gzalo/ncomputing-l130/pcb/l130.kicad_sch

## KiCad design pcb/l130.kicad_sch (2023-08-18, an earlier design)

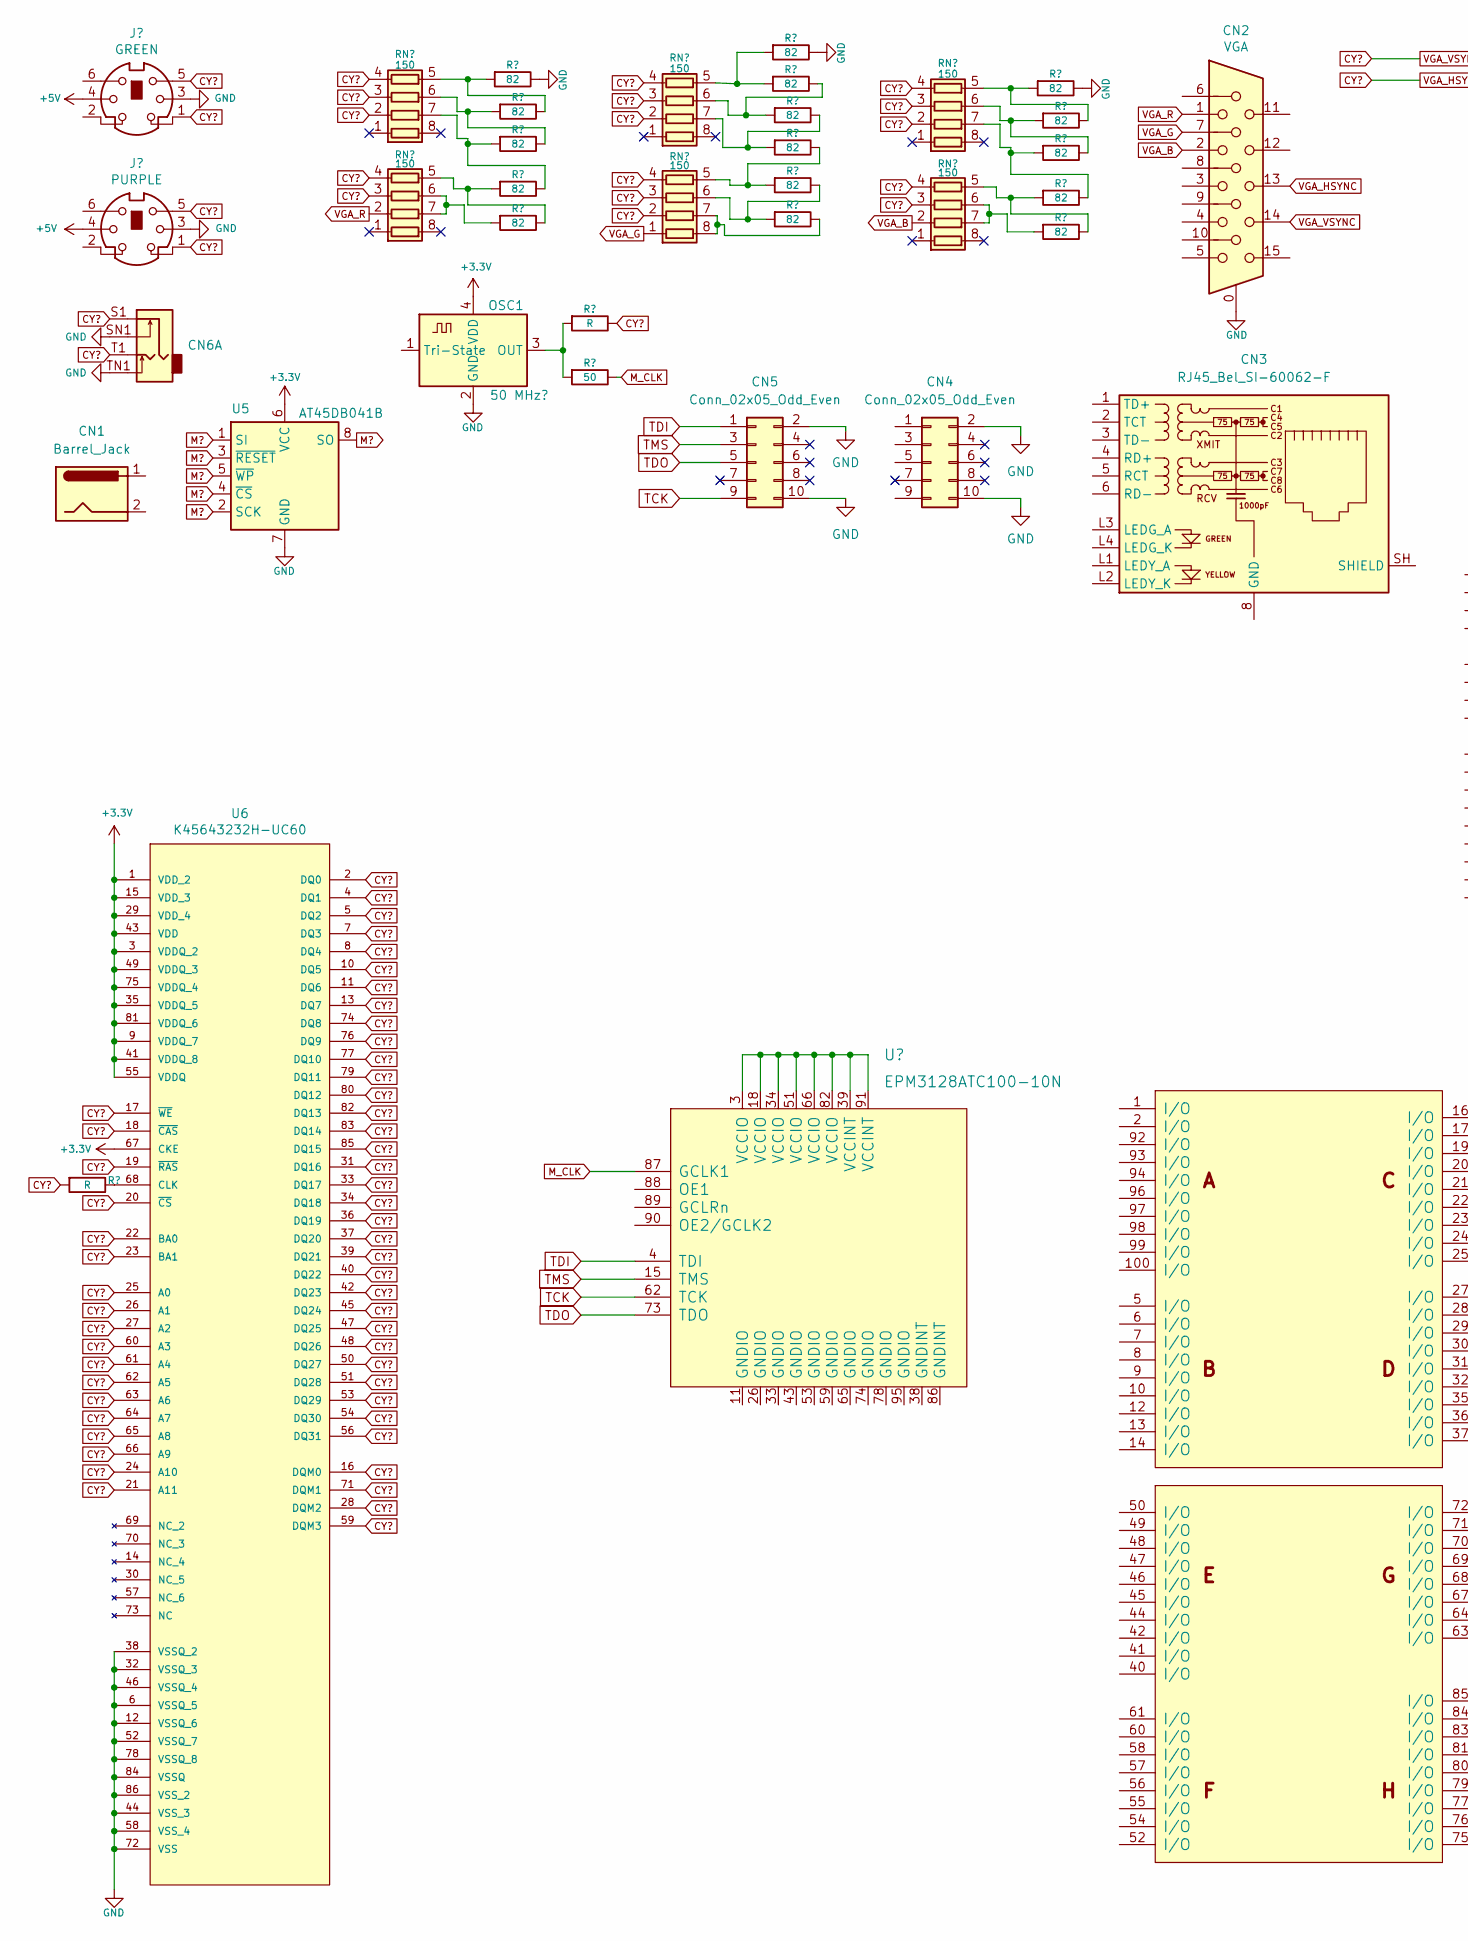
[picture p23: schematic l130.kicad_sch, part in row 1, column 1]

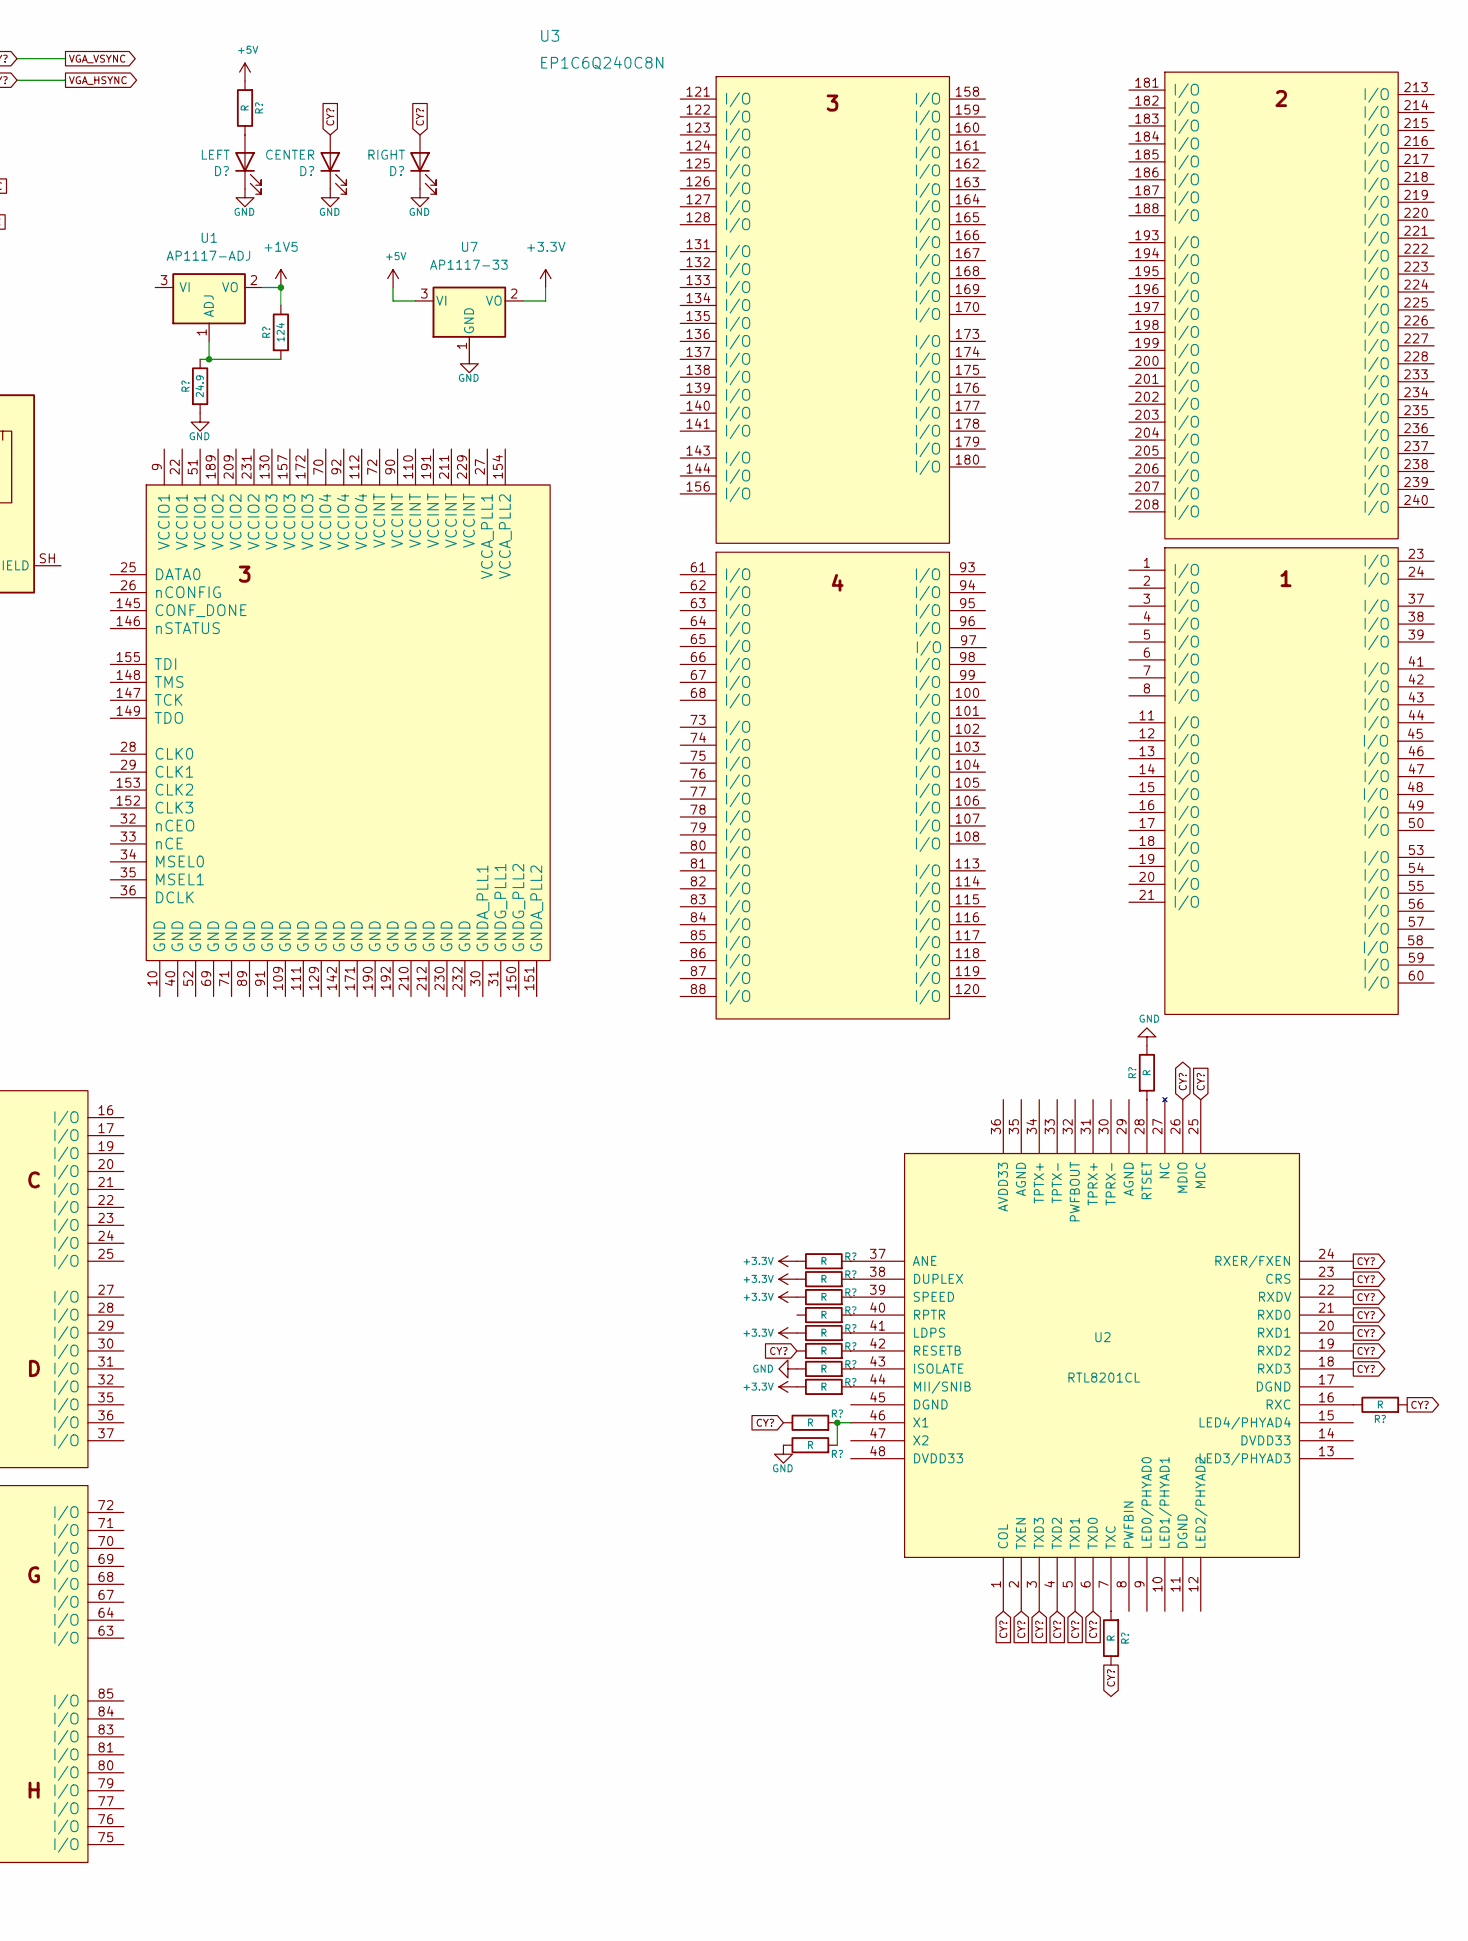
[picture p24: schematic l130.kicad_sch, part in row 1, column 2]

Parts:
CN1: Barrel_Jack
CN2: VGA
CN3: RJ45_Bel_SI-60062-F
CN4, CN5: Conn_02x05_Odd_Even
CN6: AudioJack2_Dual_Switch
OSC1: 50 MHz?; Oscillator_SMD_Abracon_ASCO-4Pin_1.6x1.2mm
U1: AP1117-ADJ; SOT-223-3_TabPin2
U2: RTL8201CL; MODULE
U3: EP1C6Q240C8N
U5: AT45DB041B; SOIC-8_5.275x5.275mm_P1.27mm
U6: K45643232H-UC60; SOP50P1176X120-86N
U7: AP1117-33; SOT-223-3_TabPin2

Connections:
CY?: CN2.13, CN2.14, CN6.S1, CN6.T1, U2.1 (COL), U2.2 (TXEN), U2.3 (TXD3), U2.4 (TXD2), U2.5 (TXD1), U2.6 (TXD0), U2.18 (RXD3), U2.19 (RXD2), U2.20 (RXD1), U2.21 (RXD0), U2.22 (RXDV), U2.23 (CRS), U2.24 (RXER/FXEN), U2.25 (MDC), U2.26 (MDIO), U6.2 (DQ0), U6.4 (DQ1), U6.5 (DQ2), U6.7 (DQ3), U6.8 (DQ4), U6.10 (DQ5), U6.11 (DQ6), U6.13 (DQ7), U6.16 (DQM0), U6.17 (~WE), U6.18 (~CAS), U6.19 (~RAS), U6.20 (~CS), U6.21 (A11), U6.22 (BA0), U6.23 (BA1), U6.24 (A10), U6.25 (A0), U6.26 (A1), U6.27 (A2), U6.28 (DQM2), U6.31 (DQ16), U6.33 (DQ17), U6.34 (DQ18), U6.36 (DQ19), U6.37 (DQ20), U6.39 (DQ21), U6.40 (DQ22), U6.42 (DQ23), U6.45 (DQ24), U6.47 (DQ25), U6.48 (DQ26), U6.50 (DQ27), U6.51 (DQ28), U6.53 (DQ29), U6.54 (DQ30), U6.56 (DQ31), U6.59 (DQM3), U6.60 (A3), U6.61 (A4), U6.62 (A5), U6.63 (A6), U6.64 (A7), U6.65 (A8), U6.66 (A9), U6.71 (DQM1), U6.74 (DQ8), U6.76 (DQ9), U6.77 (DQ10), U6.79 (DQ11), U6.80 (DQ12), U6.82 (DQ13), U6.83 (DQ14), U6.85 (DQ15)
M?: U5.1 (SI), U5.2 (SCK), U5.3 (~RESET), U5.4 (~CS), U5.5 (~WP), U5.8 (SO)
unnamed: U6.1 (VDD_2), U6.3 (VDDQ_2), U6.9 (VDDQ_7), U6.15 (VDD_3), U6.29 (VDD_4), U6.35 (VDDQ_5), U6.41 (VDDQ_8), U6.43 (VDD), U6.49 (VDDQ_3), U6.55 (VDDQ), U6.75 (VDDQ_4), U6.81 (VDDQ_6)
unnamed: U6.6 (VSSQ_5), U6.12 (VSSQ_6), U6.32 (VSSQ_3), U6.38 (VSSQ_2), U6.44 (VSS_3), U6.46 (VSSQ_4), U6.52 (VSSQ_7), U6.58 (VSS_4), U6.72 (VSS), U6.78 (VSSQ_8), U6.84 (VSSQ), U6.86 (VSS_2)
TCK: CN5.9
TDI: CN5.1
TDO: CN5.5
TMS: CN5.3
VGA_B: CN2.2
VGA_G: CN2.7
VGA_R: CN2.1
