gzalo/ncomputing-l130/pin-flex/pin-flex.kicad_sch

## KiCad design pin-flex/pin-flex.kicad_sch (2025-07-04)

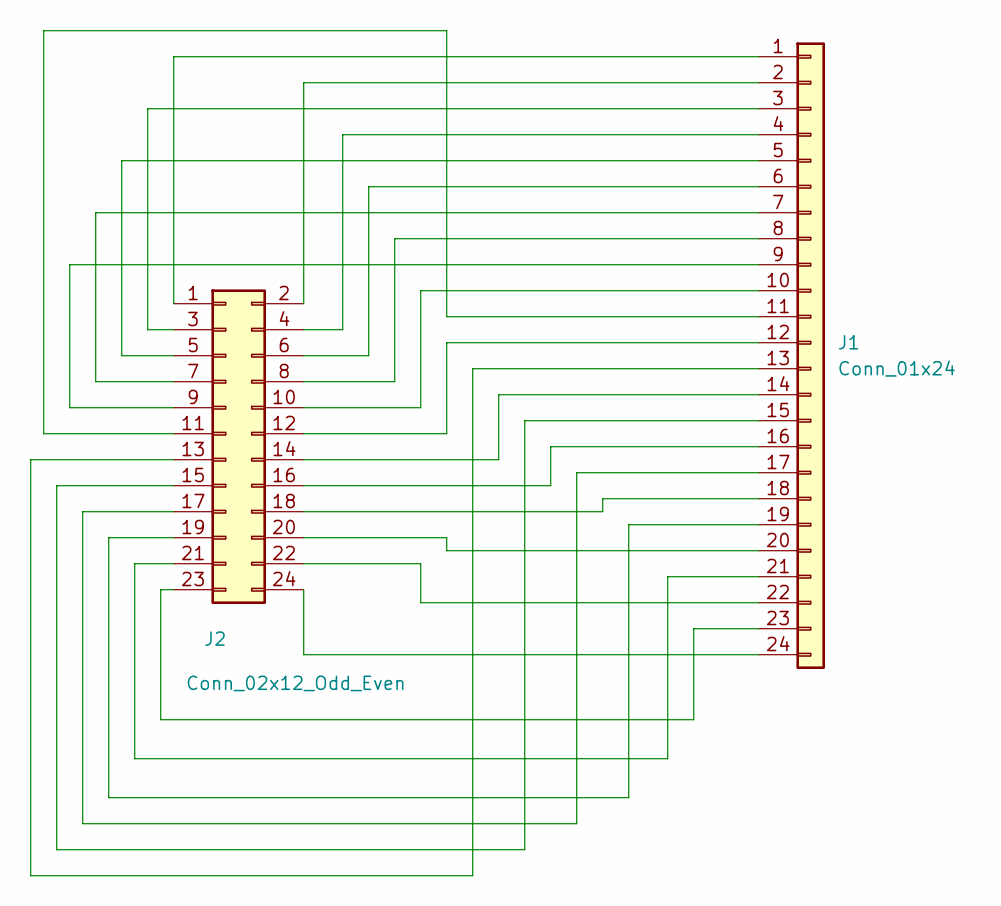
[picture p25: schematic pin-flex.kicad_sch]

Parts:
J1: Conn_01x24; 24-pin-0.5
J2: Conn_02x12_Odd_Even; PinHeader_2x12_P2.54mm_Vertical

Connections:
unnamed: J1.1, J2.1
unnamed: J1.2, J2.2
unnamed: J1.3, J2.3
unnamed: J1.4, J2.4
unnamed: J1.5, J2.5
unnamed: J1.6, J2.6
unnamed: J1.7, J2.7
unnamed: J1.8, J2.8
unnamed: J1.9, J2.9
unnamed: J1.10, J2.10
unnamed: J1.11, J2.11
unnamed: J1.12, J2.12
unnamed: J1.13, J2.13
unnamed: J1.14, J2.14
unnamed: J1.15, J2.15
unnamed: J1.16, J2.16
unnamed: J1.17, J2.17
unnamed: J1.18, J2.18
unnamed: J1.19, J2.19
unnamed: J1.20, J2.20
unnamed: J1.21, J2.21
unnamed: J1.22, J2.22
unnamed: J1.23, J2.23
unnamed: J1.24, J2.24
