gzalo/ncomputing-l130/fpga_vga/char_rom.vhd

library ieee;
use ieee.std_logic_1164.all;
use ieee.numeric_std.all;

entity char_rom is
	port(
		clk: in std_logic;
		char: in std_logic_vector(3 downto 0); --16 chars
		posX: in std_logic_vector(4 downto 0); -- position within the char (32x32)
		posY: in std_logic_vector(4 downto 0); -- position within the char (32x32)
		valueout: out std_logic
	);
end;

architecture behavioral of char_rom is
type rom_type is array(0 to 511) of std_logic_vector(0 to 31);
signal ROM: rom_type:= (
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
signal posXRom: std_logic_vector(4 downto 0);
begin
	rom_addr <= unsigned(char) & unsigned(posY);

	process(clk)
	begin
		if rising_edge(clk) then
			memvalue <= ROM(to_integer(rom_addr));
			posXRom <= posX;
		end if;
	end process;

	valueout <= memvalue(to_integer(unsigned(posXRom)));
end;
